ka6s/fp2/fp2/swaper/swaper.kicad_pcb

## KiCad design schematics/kicad/ele.sch

Schematic: ele.sch

Parts:
C1, C2, C3, C4, C5, C6, C7, C8: 0.1uF; C_Rect_L4.6mm_W2.0mm_P2.50mm_MKS02_FKP02
C9: 10uF/10V; CP_Radial_Tantal_D4.5mm_P2.50mm
D1: 1N4004
F1: Fuse; Fuseholder_Cylinder-5x20mm_Schurter_0031_8201_Horizontal_Op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
J1: CONN_MOT_BUMB_R; PinHeader_1x02_P2.54mm_Vertical
J2: CONN_MOT_BUMB_L; PinHeader_1x02_P2.54mm_Vertical
J3: CONN_UI
J4: Conn_MOT1
J5: Conn_MOT2
J6: CONN_POWER_IN; TerminalBlock_bornier-2_P5.08mm
J7: Conn_MOT_OUT
Q1, Q2, Q3: 2N3904
Q4: LQP30N
R1, R2, R5, R6, R15, R16: 1K; R_Axial_DIN0204_L3.6mm_D1.6mm_P2.54mm_Vertical
R3, R4, R8, R13, R14: 10K; R_Axial_DIN0204_L3.6mm_D1.6mm_P2.54mm_Vertical
R7: 100K; R_Axial_DIN0204_L3.6mm_D1.6mm_P2.54mm_Vertical
R9: 40k; R_Axial_DIN0204_L3.6mm_D1.6mm_P2.54mm_Vertical
R10: 100; R_Axial_DIN0204_L3.6mm_D1.6mm_P2.54mm_Vertical
R11, R12: 50
R17, R18, R19: 10k
SW1: SW_Push
U1: ACS712_MODULE; PinHeader_1x03_P2.54mm_Vertical
U2: VS1838B; TO-92_Inline
U3: STM32BLUEPILL
U4: LM2596_DC_DC_BUCK_MODULE
U5: MOTOSHIELD
U6: LD1117S33TR; TO-220-3_Vertical
